jp112sdl/HB-Dis-EP-42BW/3D_Druck/Images/2.JPG

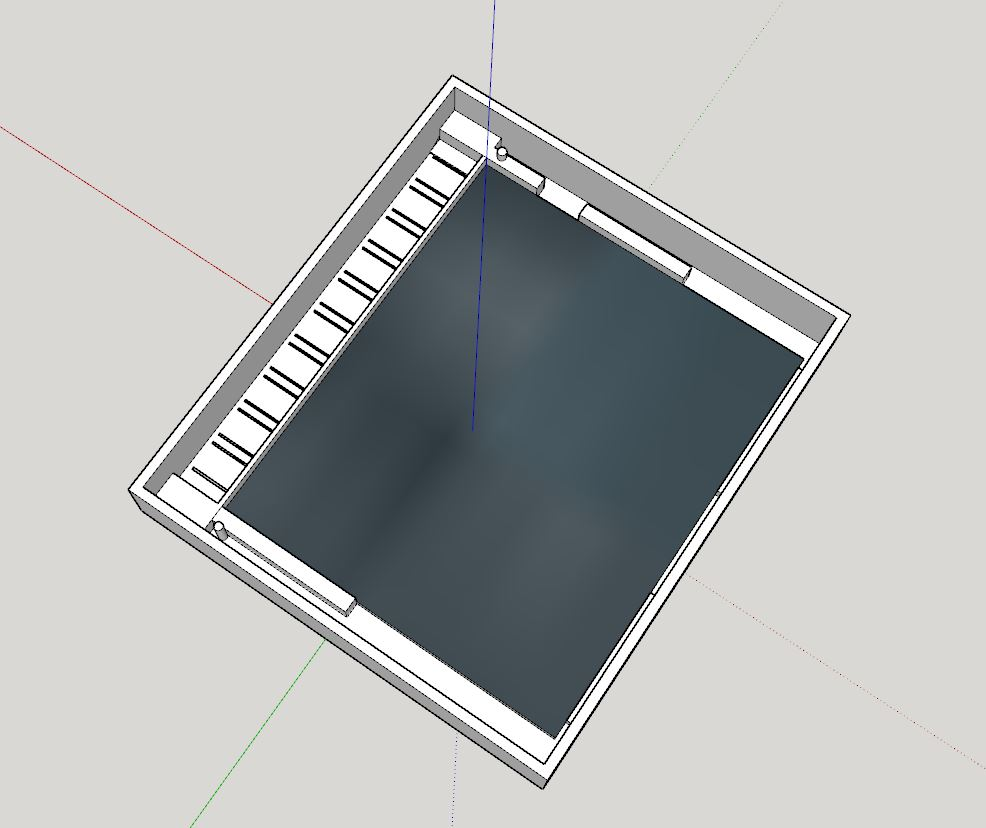
3D_Druck/Images/2.JPG
