jp112sdl/HB-Dis-EP-42BW/3D_Druck/Images/IMG_20190317_192404.jpg

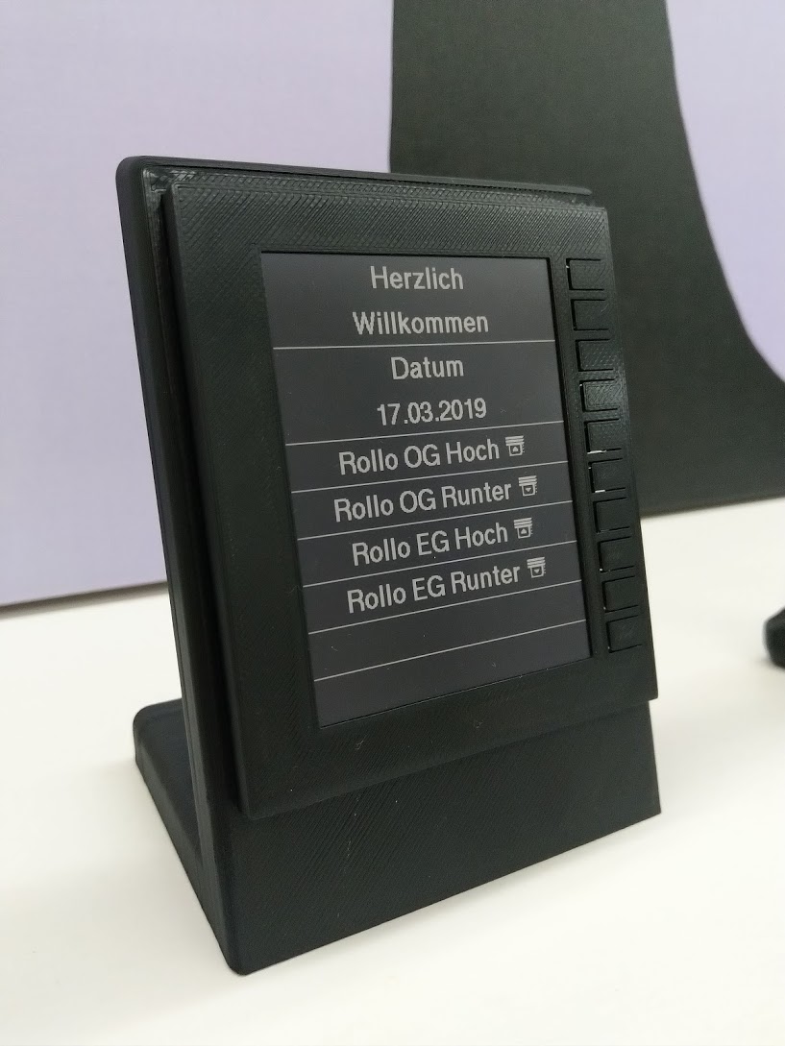
3D_Druck/Images/IMG_20190317_192404.jpg
