jp112sdl/HB-Dis-EP-42BW/Images/IMG_9059.jpg

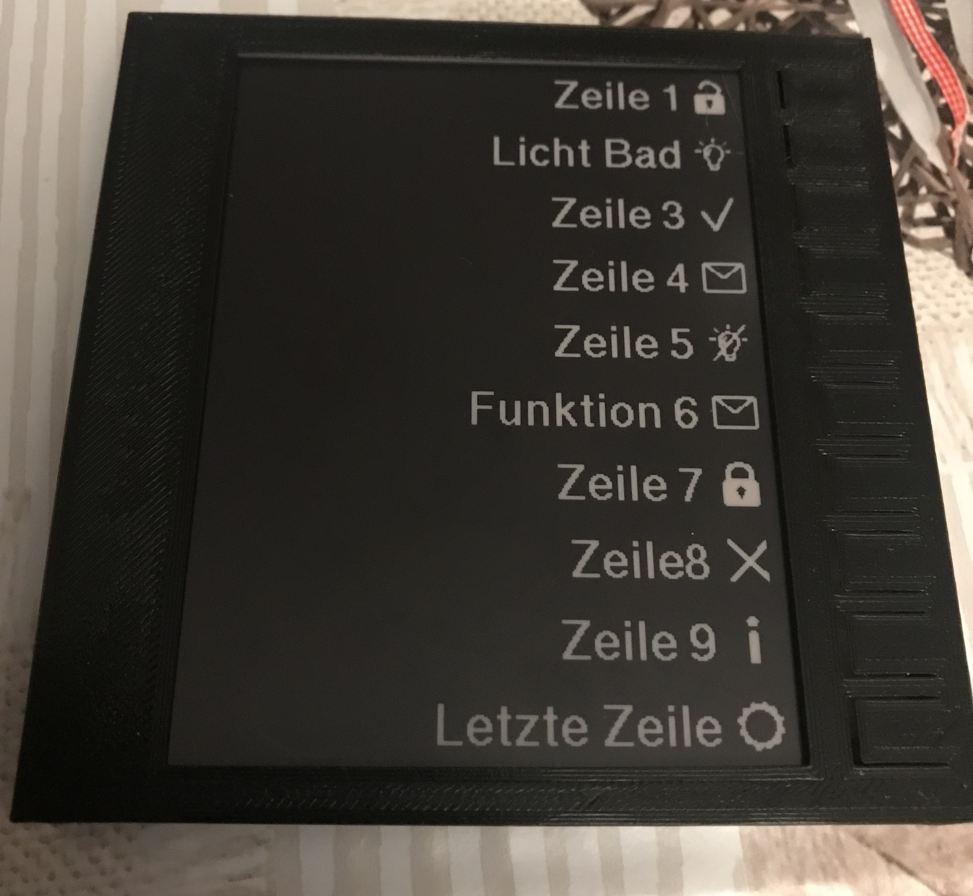
Images/IMG_9059.jpg
