jp112sdl/HB-Dis-EP-42BW/Images/IMG_9084.jpg

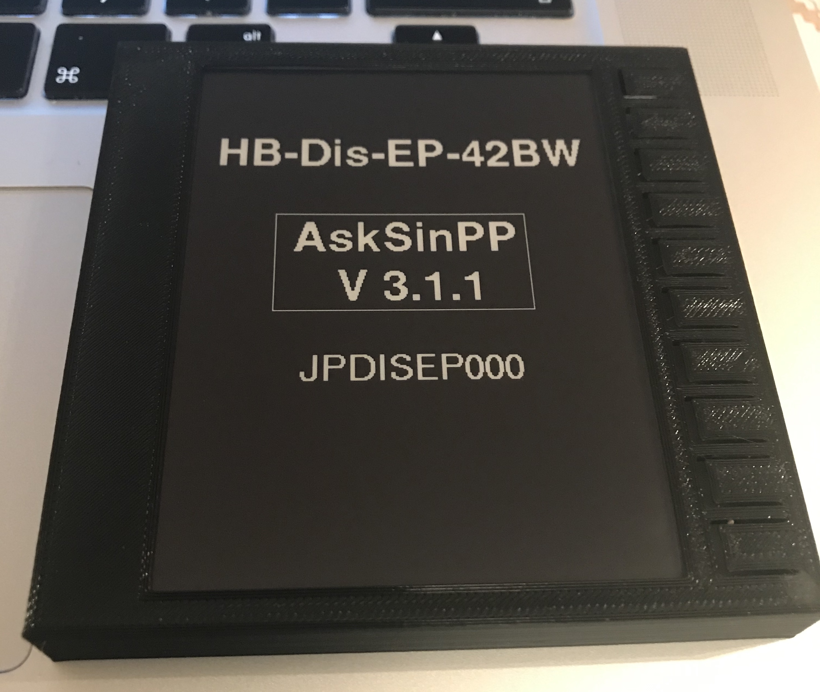
Images/IMG_9084.jpg
