jp112sdl/HB-Dis-EP-42BW/Images/IMG_9178.jpg

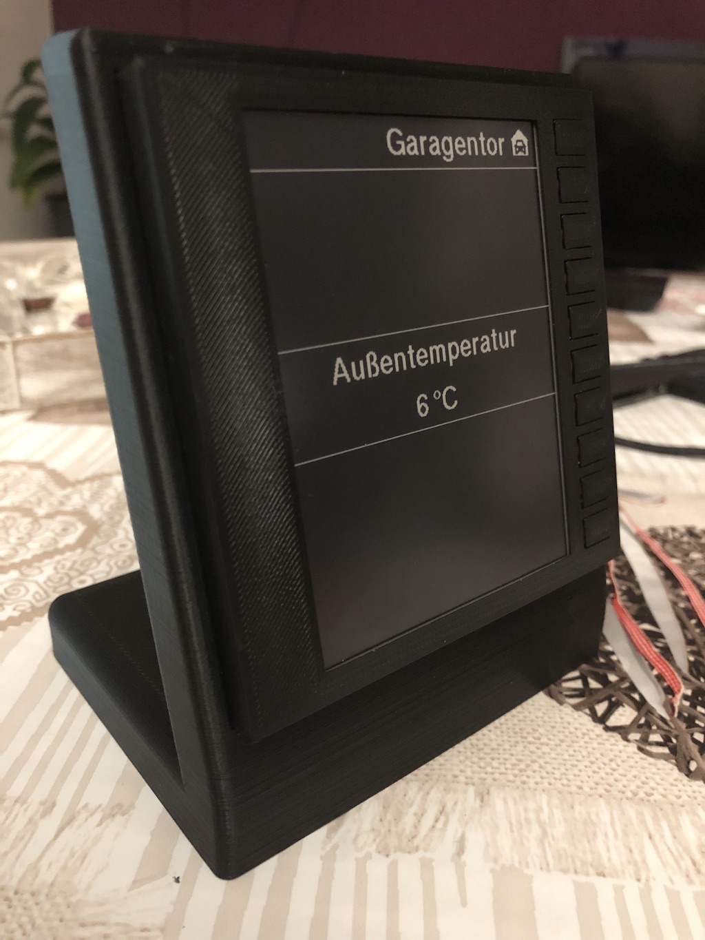
Images/IMG_9178.jpg
